HarvardURC/Pacbot/src/botCode/low_level/motor.py

from .GPIOhelpers import *
from enum import Enum
from time import sleep
setGPIO()

class MotorDirection(Enum):
    BACKWARD = 0
    FORWARD = 1
    STOP = 2

class Motor:
    def __init__(self, name, power_pin, direction_pin, speed = 0):
        self.name = name
        self.power_pin = power_pin
        self.direction_pin = direction_pin
        self.speed = speed
        analogMode(self.power_pin, 0)
        digitalMode(self.direction_pin, OUTPUT)

    def move(self, direction, speed):
        if direction == MotorDirection.STOP:
            analogWrite(self.power_pin, 0)
        else:
            #print(str(self.name))
            #print(" motor moving ")
            #if direction == MotorDirection.BACKWARD:
                #print("backwards")
            #else:
                #print("forwards")
            #print("...\n")
            #print(direction.value)
            if self.name == "Right":
                digitalWrite(self.direction_pin, (direction.value + 1) % 2)
            else:
                digitalWrite(self.direction_pin, direction.value)
            analogWrite(self.power_pin,speed)

    def stop(self):
        analogWrite(self.power_pin,0)
        digitalWrite(self.direction_pin, 0)
            #GPIO.setup(10, OUTPUT)
            #pwm = GPIO.PWM(10, 490)
            #pwm.start(90)
            #sleep(3)
