HarvardURC/Pacbot/src/botCode/low_level/legends.py

# Wall
I = 1

# Unreachable
e = 2

# Untouchable
n = 3

""" Corner
I,I,I
o,c,I
I,o,I
"""
c = 4

""" Straight tunnel
I,I,I
o,s,o
I,I,I
"""
s = 5

""" Tri-junction A
I,I,I
j,o,o
I,o,I
"""
j = 6

""" Tri-junction B
I,I,I
o,o,o
I,k,I
"""
k = 7

""" Tri-junction Main
I,I,I
o,l,o
I,o,I
"""
l = 8

""" Crossroads
I,o,I
o,r,o
I,o,I
"""
r = 9
